hackersanddesigners/hackedorchestra_teensy/code/example sketches/Part_2_02_Mixers/2_02_Mixers.png

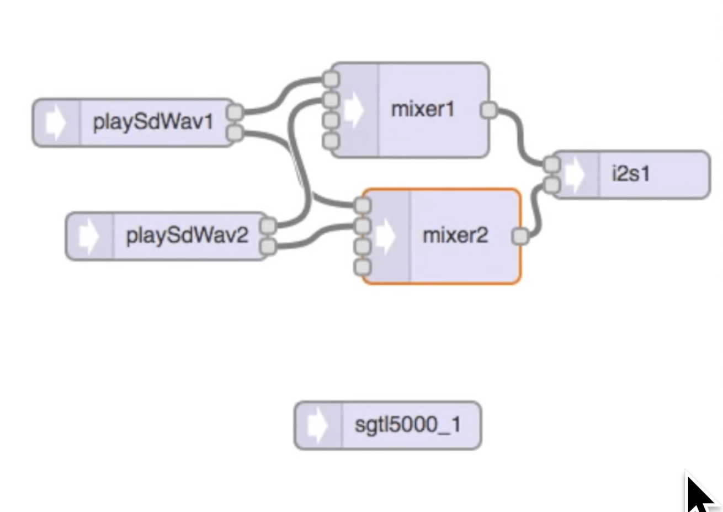
code/example sketches/Part_2_02_Mixers/2_02_Mixers.png
