hackersanddesigners/hackedorchestra_teensy/code/example sketches/Part_2_03_Samples/2_03_Samples.png

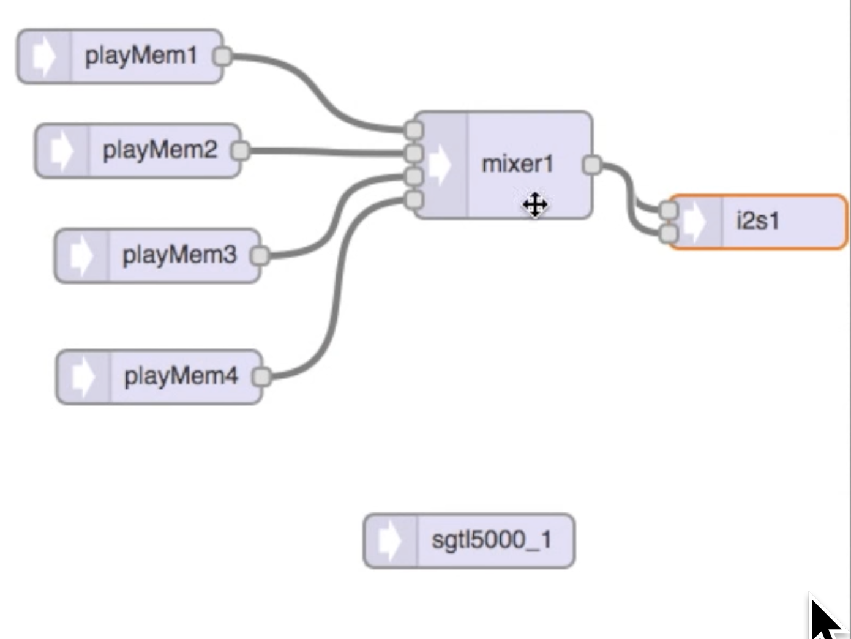
code/example sketches/Part_2_03_Samples/2_03_Samples.png
