hackersanddesigners/hackedorchestra_teensy/code/example sketches/Part_2_04_Microphone_Check/2_04_Microphone_check.png

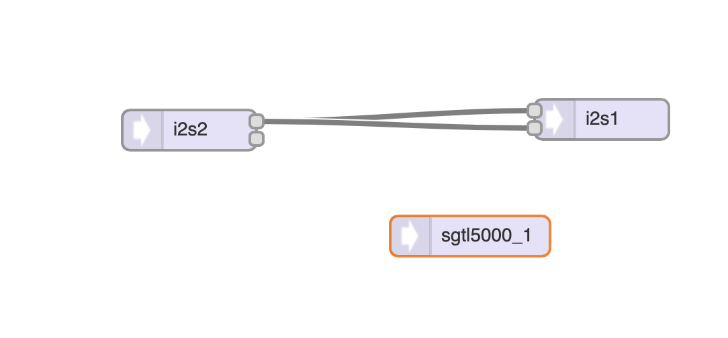
code/example sketches/Part_2_04_Microphone_Check/2_04_Microphone_check.png
