hackersanddesigners/hackedorchestra_teensy/code/example sketches/Part_2_05_Simple_Delay/2_05_SimpleDelay.png

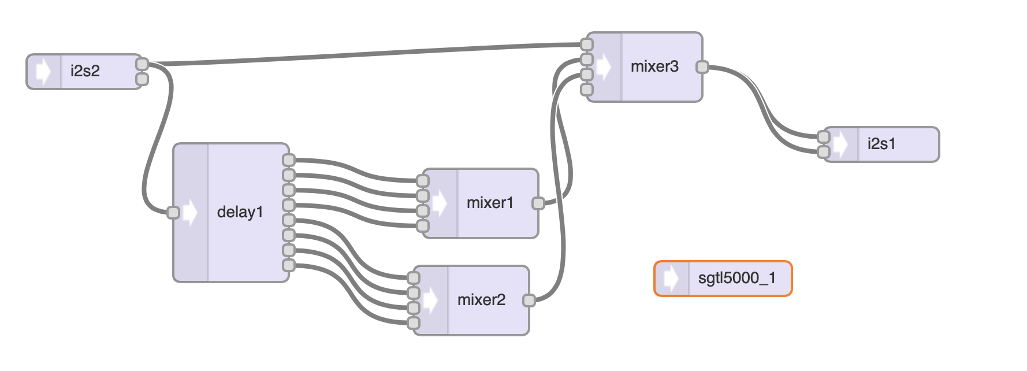
code/example sketches/Part_2_05_Simple_Delay/2_05_SimpleDelay.png
