hackersanddesigners/hackedorchestra_teensy/code/example sketches/Part_2_06_Feedback_Delay/2_06_Feedback_Delay.png

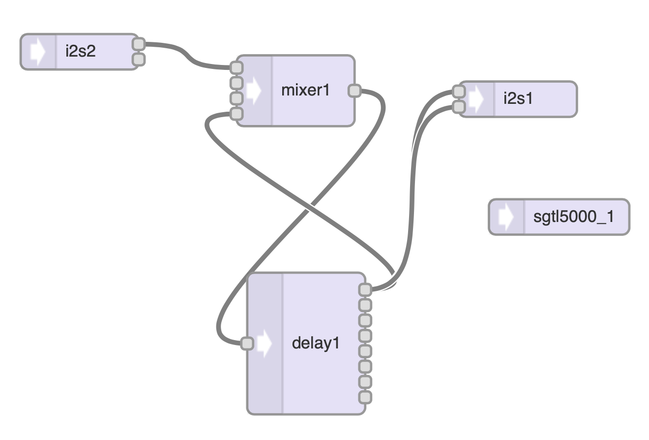
code/example sketches/Part_2_06_Feedback_Delay/2_06_Feedback_Delay.png
