hackersanddesigners/hackedorchestra_teensy/code/example sketches/Part_2_07_Filters/2_07_Filters.png

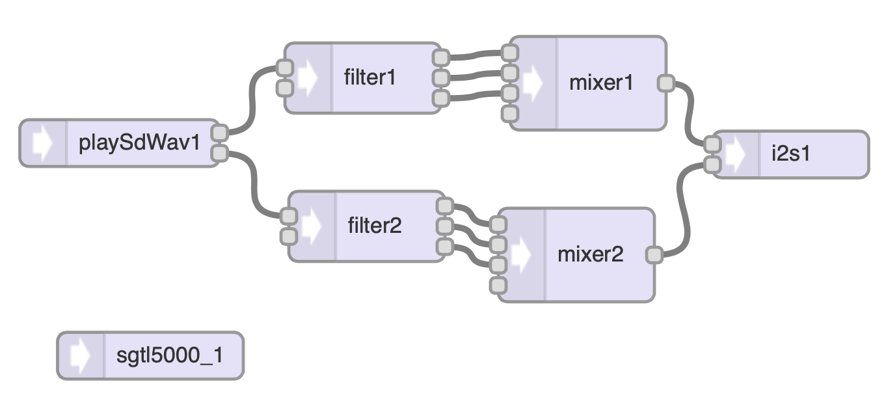
code/example sketches/Part_2_07_Filters/2_07_Filters.png
