hackersanddesigners/hackedorchestra_teensy/code/example sketches/Part_2_08_Oscillators/2_08_Oscillators_Envelope.png

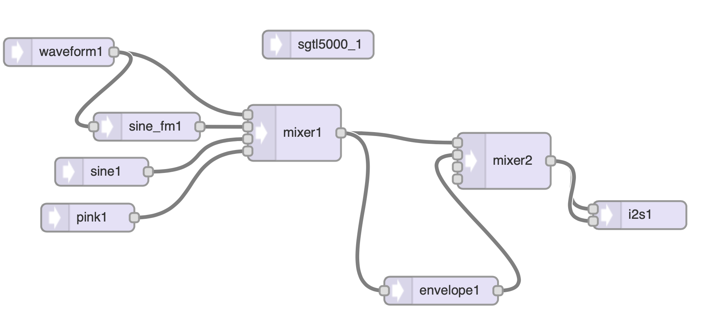
code/example sketches/Part_2_08_Oscillators/2_08_Oscillators_Envelope.png
