hackersanddesigners/hackedorchestra_teensy/code/example sketches/Part_3_01_Peak_Detection/3_01_PeakDetection.png

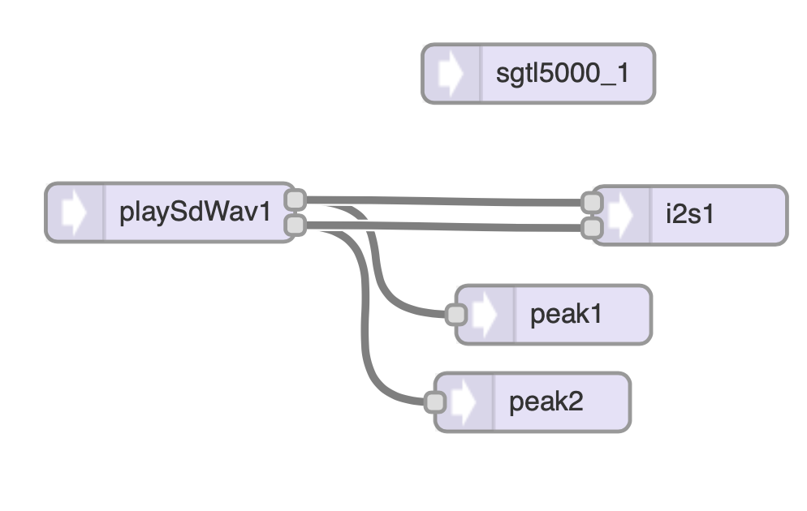
code/example sketches/Part_3_01_Peak_Detection/3_01_PeakDetection.png
