hackersanddesigners/hackedorchestra_teensy/code/example sketches/Part_3_02_Fourier_Transform/3_02_FourierTransform.png

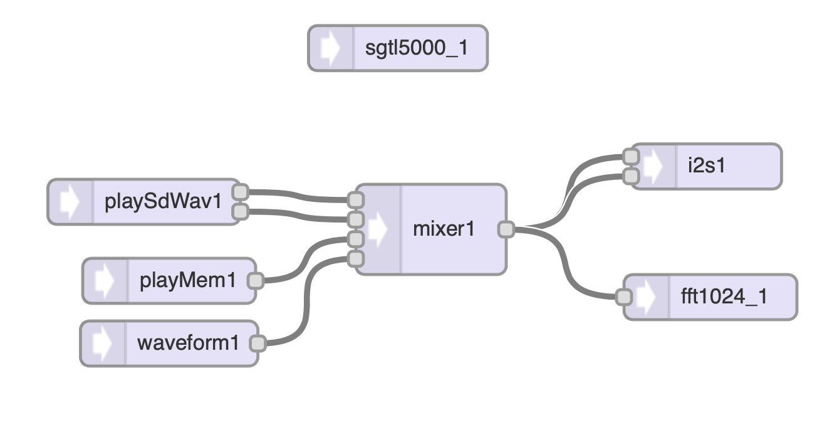
code/example sketches/Part_3_02_Fourier_Transform/3_02_FourierTransform.png
