hackersanddesigners/hackedorchestra_teensy/code/example sketches/Part_3_03_TFT_Display/3_03_TFT_Display.png

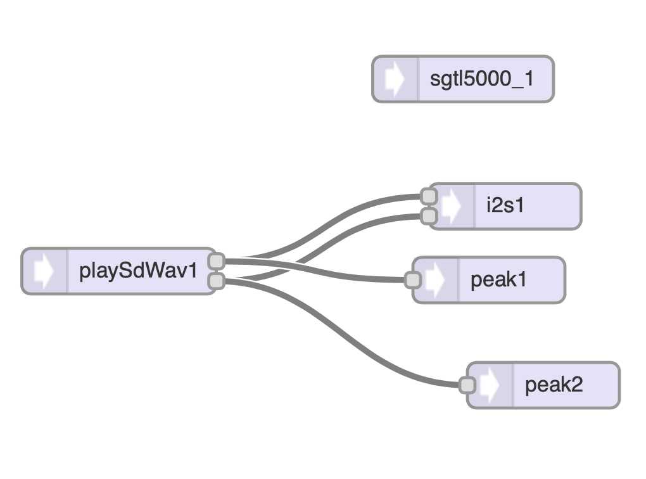
code/example sketches/Part_3_03_TFT_Display/3_03_TFT_Display.png
