hackersanddesigners/hackedorchestra_teensy/code/granular_pitch/granular_pitch.png

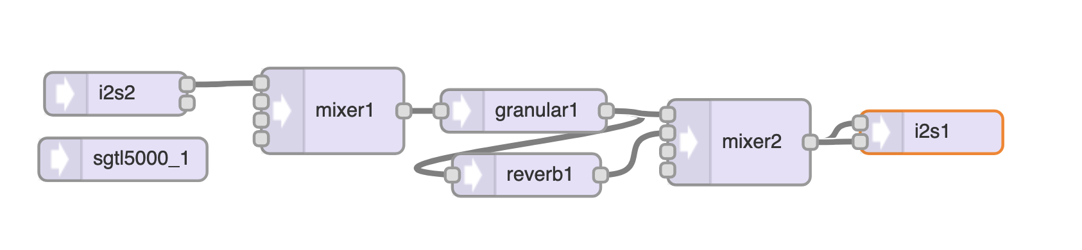
code/granular_pitch/granular_pitch.png
