hackersanddesigners/hackedorchestra_teensy/files/booklet_kids1.jpeg

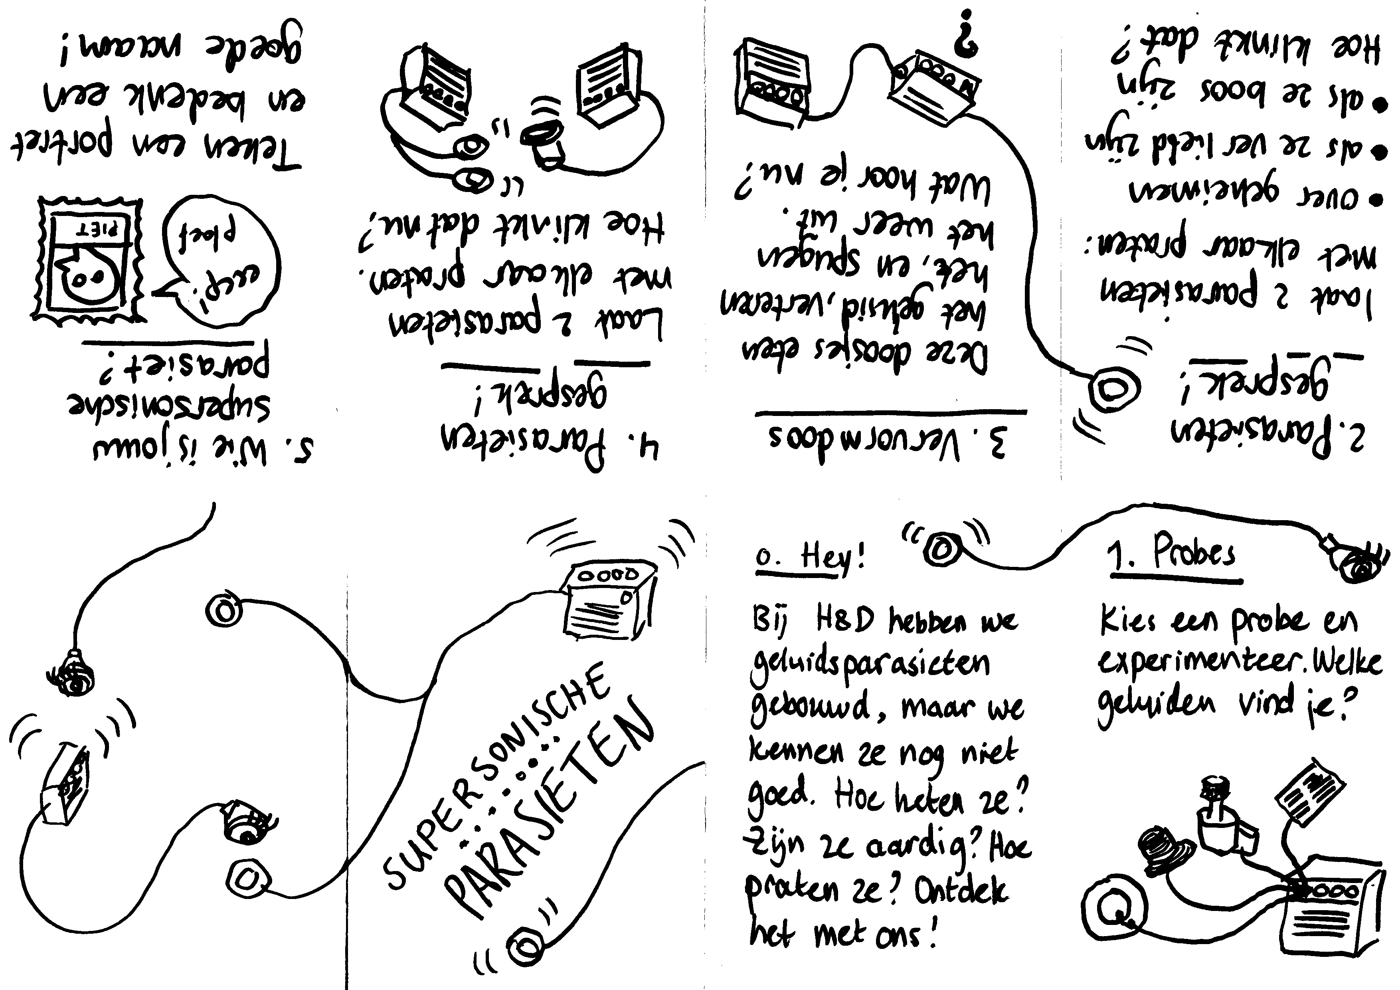
files/booklet_kids1.jpeg
