hackersanddesigners/hackedorchestra_teensy/files/booklet_kids2.jpeg

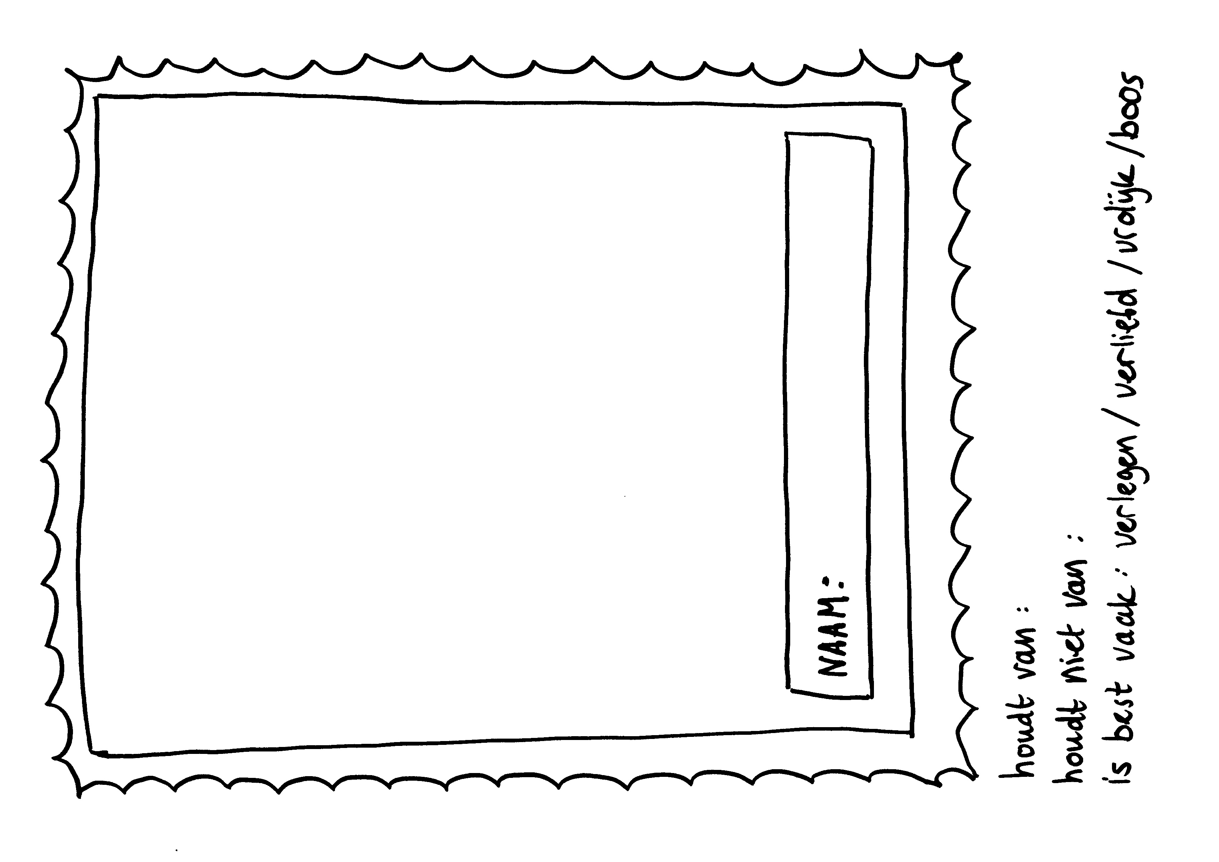
files/booklet_kids2.jpeg
