hackersanddesigners/hackedorchestra_teensy/images/fritz1.jpg

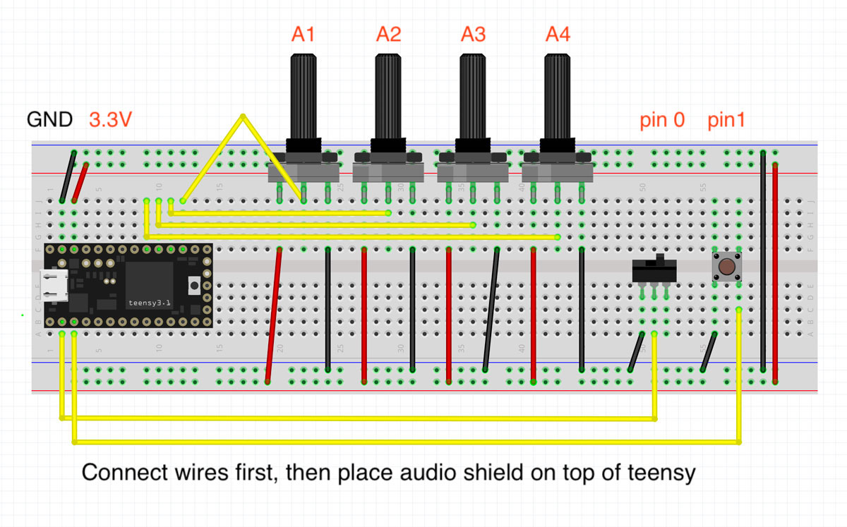
images/fritz1.jpg
