hackersanddesigners/hackedorchestra_teensy/images/jack_holder_volkan_dincer.png

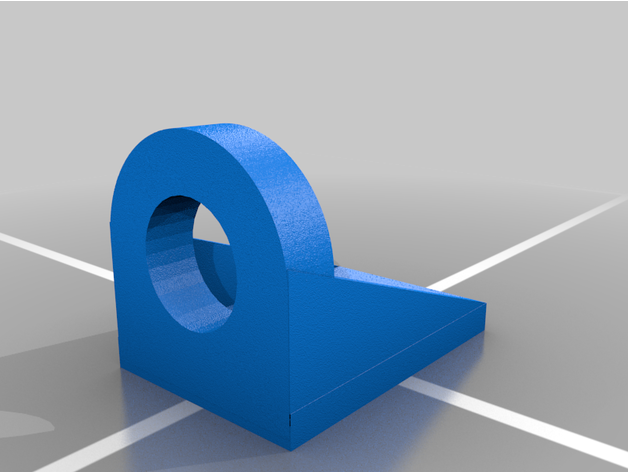
images/jack_holder_volkan_dincer.png
