hackersanddesigners/hackedorchestra_teensy/images/placeholder.png

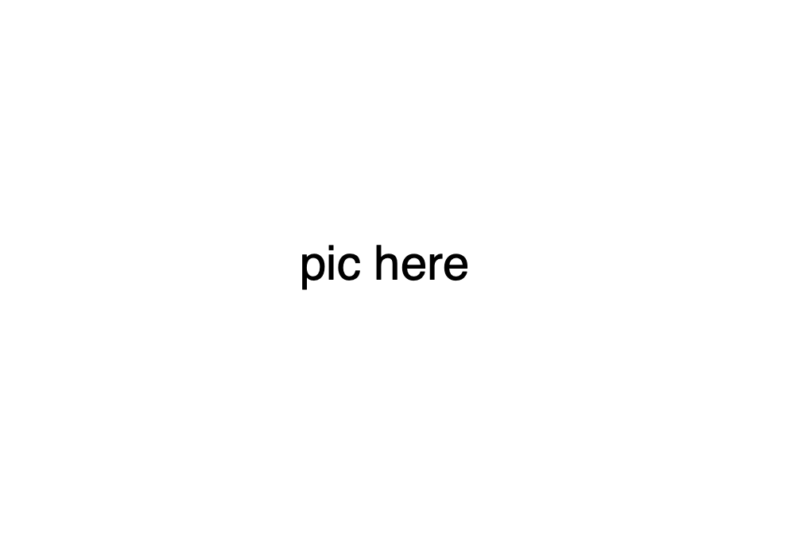
images/placeholder.png
