hackersanddesigners/hackedorchestra_teensy/code/example sketches/Part_2_03_Samples/AudioSampleGong.cpp

// Audio data converted from WAV file by wav2sketch

#include "AudioSampleGong.h"

// Converted from gong.wav, using 11025 Hz, u-law encoding
const unsigned int AudioSampleGong[27633] = {
0x0301AFA4,0x00000000,0x00000000,0x00000000,0x00000000,0x00000000,0x00000000,0x00000000,
0x00000000,0x00000000,0x00000000,0x00000000,0x00008000,0x00000000,0x00000000,0x80800000,
0x00000000,0x00000000,0x00000080,0x00000000,0x00000000,0x00000000,0x00000080,0x00000000,
0x00000000,0x00000000,0x00000000,0x00000000,0x00000000,0x00000000,0x00000000,0x00000000,
0x00008000,0x00000000,0x00000000,0x00000000,0x00000000,0x00000080,0x00000000,0x00000000,
0x00000000,0x00000080,0x00000000,0x00000000,0x00000000,0x00000000,0x00000000,0x00000000,
0x00000000,0x00000000,0x00000080,0x00000000,0x00000000,0x00000000,0x00000000,0x00008000,
0x81008000,0x0F0D100A,0x0C0B0D0C,0x24110C0A,0x655C4F3D,0x7775726D,0x74767778,0xBD556770,
0xF4F2EBE0,0xEAEFF3F5,0xE8E7E6E7,0xEDEEEDEB,0xEAEAEAEB,0xE6E8EAEA,0xCCD9E1E4,0x62584897,
0x6D6C6966,0x71706E6D,0x676F7172,0xE8DEB557,0xE6EAEDED,0xD2D8DEE2,0x431DB8C7,0x5252514C,
0x5F5C5754,0x61626261,0x5656585D,0x65625E59,0x66666766,0x5B616466,0xE0D1964E,0xF0EDE9E5,
0xEEF0F1F0,0xDFE3E8EC,0xD3D5D7DA,0xB1BCC5CE,0xC3B7B1A9,0xD5D5D2CC,0xC7C5C9D1,0xD3D5D3CD,
0xCBC9CCD1,0xDEDCD8D2,0xAFCED8DD,0x615B5241,0x68686764,0x63656768,0x64636161,0x40566164,
0xDCDBD5C0,0xCCD2D7DB,0xBFC3C5C7,0x6055448C,0x6B6B6965,0x5A606468,0x96404E55,0xCECEC9C0,
0x2FB2C6CC,0x3C454843,0xD0B71131,0xE8E8E4DD,0xD7DDE2E6,0xE2DCD6D4,0xEDECE9E6,0xE4E8EBED,
0x90C6D6E0,0x534F483D,0x615F5B57,0x5F636363,0xCBBC3352,0xB9C1C9CE,0xD2CCC2B9,0x4B85C7D1,
0x6A67625A,0x64676A6B,0x595A5D60,0x5F5F5C59,0xCB2E525B,0xE2E4E3DC,0x5342BCD8,0x53575959,
0x4A4E5152,0x443E3C43,0xBA233E43,0xE9E6E0D2,0xCDDCE4E9,0x534F41A0,0x4E535555,0xC1A33244,
0xEEE5DBD0,0xF8F8F6F3,0xE1EBF2F6,0x4226BDD3,0x66615850,0x6F70706B,0x555D646A,0xB31C424F,
0xB4BBC0C0,0xBEA997A7,0xD1D3D2CC,0x4D37B3C9,0x55555654,0x63605C57,0x5F626464,0x6363605E,
0x27445560,0x4C473617,0xD6C80445,0x42C1D5DA,0x44545955,0xE1D9CDAB,0xE8E8E8E5,0xE3E4E5E7,
0xE0E0E1E2,0xBFD4DBDF,0x615F5640,0xB444565F,0xE1E0DBD2,0xE4E5E4E3,0xD6DDE2E3,0x4681BFCE,
0x6D696359,0x656A6E6F,0x63615F61,0x36566164,0xDDD9D2C3,0xBBCFD7DC,0xB8A8078B,0x4F4118B4,
0x6A666056,0x6165686A,0x3E46525B,0xD1B62734,0xD8E1E2DD,0x2D24A4C6,0x1BABA11F,0x595A5647,
0x123D4A54,0xE7E0D1BC,0xF7F4F1EC,0xE7F1F5F7,0x3B23C4DC,0x45414040,0x645C524A,0x656B6C6A,
0xE7DEB655,0xDBE2E7E9,0xC4C0C6D2,0x4AA0C5C9,0x6968645C,0x5C606467,0x5256585A,0x3130404B,
0xB8253A37,0xD8D9D6CF,0x5D4AB0D0,0x62656664,0x62615E5F,0x505A6062,0xE0D6C42E,0xE6E8E7E5,
0x24C7DAE3,0xC4A53B43,0x533AB5C6,0x4A5C615E,0xEDE9E0C4,0xEFEFEFEE,0xE3E6EAED,0xB8CCD7DF,
0x52453817,0x60605E59,0x585F6261,0x453A4150,0x48575853,0xE3DED4B7,0xD2DEE2E4,0x595347A2,
0x63656460,0x68656261,0x43566267,0xD3D2C9A9,0x85AAC2CE,0xC4C4BDA8,0x38A8BBC0,0x5C5D5A51,
0x52585C5C,0x323F4349,0xCEC0A320,0xE3E2DED6,0xE6E5E4E3,0xC8D4DFE4,0x3223A1BA,0xBBA71330,
0xB6B2C1C5,0xE2E1DBCE,0x27B8CFDB,0x424A4A42,0xAA9E2036,0x534121A3,0x5E646560,0x9A1D334D,
0xB1C6C9BF,0xD0BB2021,0xBECED5D6,0x6560522E,0x67676666,0x4F5F6466,0xD0D8D4B3,0xC5A880B8,
0xD2D9D8D2,0x635C4CAB,0x4C586265,0x58534A45,0xC11B4654,0xE3E1DED4,0xF0EEE9E5,0xD3E2EBF0,
0xC0BBB6C2,0xBEC1B9BC,0x595C5433,0x514D4B52,0xC8B6324C,0xE1E1DFD5,0xD8D9DADE,0x31C0D0D5,
0x6B696254,0x5C626568,0x59534F53,0xCB994C59,0xDDE2E1D8,0xBCCCD0D3,0x57534F38,0x6164635E,
0x615D5A5B,0x435A6263,0xE5E0D4BE,0xDAE4E8E8,0x2900ADC9,0x615D5241,0x5E606162,0xC22F4D58,
0xEBE6E0D5,0xE9ECF0EF,0xE0E7E9E9,0x3D82BDD2,0x453D4749,0x60605D54,0x545B6060,0x3D484C50,
0xD8D3C401,0xE1DDDBDA,0xDAE2E5E5,0x30C1CDD2,0x67646053,0x696F6E6A,0x49555961,0x3D9BB807,
0xDDCF1744,0xE8EDEAE4,0x69603AD8,0x5D63696C,0x5E565155,0x50606262,0xDEDDD5B5,0xDED9D9DB,
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

};
