hackersanddesigners/hackedorchestra_teensy/code/example sketches/Part_2_05_Simple_Delay/Part_2_05_Simple_Delay.ino

// Advanced Microcontroller-based Audio Workshop
//
// http://www.pjrc.com/store/audio_tutorial_kit.html
// https://hackaday.io/project/8292-microcontroller-audio-workshop-had-supercon-2015
// 
// Part 2-5: Simple Delay


///////////////////////////////////
// copy the Design Tool code here
///////////////////////////////////

#include <Audio.h>
#include <Wire.h>
#include <SPI.h>
#include <SD.h>
#include <SerialFlash.h>
#include <Audio.h>
#include <Wire.h>
#include <SPI.h>
#include <SD.h>
#include <SerialFlash.h>

// GUItool: begin automatically generated code
AudioInputI2S            i2s2;           //xy=75,178
AudioEffectDelay         delay1;         //xy=202,300
AudioMixer4              mixer2;         //xy=410,376
AudioMixer4              mixer1;         //xy=418,292
AudioMixer4              mixer3;         //xy=594,195
AudioOutputI2S           i2s1;           //xy=765,241
AudioConnection          patchCord1(i2s2, 0, mixer3, 0);
AudioConnection          patchCord2(i2s2, 0, delay1, 0);
AudioConnection          patchCord3(delay1, 0, mixer1, 0);
AudioConnection          patchCord4(delay1, 1, mixer1, 1);
AudioConnection          patchCord5(delay1, 2, mixer1, 2);
AudioConnection          patchCord6(delay1, 3, mixer1, 3);
AudioConnection          patchCord7(delay1, 4, mixer2, 0);
AudioConnection          patchCord8(delay1, 5, mixer2, 1);
AudioConnection          patchCord9(delay1, 6, mixer2, 2);
AudioConnection          patchCord10(delay1, 7, mixer2, 3);
AudioConnection          patchCord11(mixer2, 0, mixer3, 2);
AudioConnection          patchCord12(mixer1, 0, mixer3, 1);
AudioConnection          patchCord13(mixer3, 0, i2s1, 0);
AudioConnection          patchCord14(mixer3, 0, i2s1, 1);
AudioControlSGTL5000     sgtl5000_1;     //xy=628,357
// GUItool: end automatically generated code


void setup() {
  Serial.begin(9600);
  AudioMemory(160);     //working with delays requires more memory allocated!
  sgtl5000_1.enable();
  sgtl5000_1.volume(0.6);
  sgtl5000_1.inputSelect(AUDIO_INPUT_MIC);
  sgtl5000_1.micGain(36);
  mixer1.gain(0, 0.2);
  mixer1.gain(1, 0.2);
  mixer1.gain(2, 0.2);
  mixer1.gain(3, 0.2);
  mixer2.gain(0, 0.2);
  mixer2.gain(1, 0.2);
  mixer2.gain(2, 0.2);
  mixer2.gain(3, 0.2);
  mixer3.gain(0, 0.0); // default = do not listen to direct signal
  mixer3.gain(1, 1.0); // ch1 is output of mixer1
  mixer3.gain(2, 1.0); // ch2 is output of mixer2
  delay1.delay(0, 400);
  delay1.delay(1, 400);
  delay1.delay(2, 400);
  delay1.delay(3, 400);
  delay1.delay(4, 400);
  delay1.delay(5, 400);
  delay1.delay(6, 400);
  delay1.delay(7, 400);
  delay(1000);
}

void loop() {

  // read the knob position (analog input A2)
  
  int knob = analogRead(A2);
  float vol = (float)knob / 1280.0;
  sgtl5000_1.volume(vol);
  Serial.print("volume = ");
  Serial.println(vol);

}
